taha-ahmed-mallick/NitroBurner-28c256/hardware/NitroBurner-28c256.kicad_sch

## KiCad design hardware/NitroBurner-28c256.kicad_sch (2026-06-18)

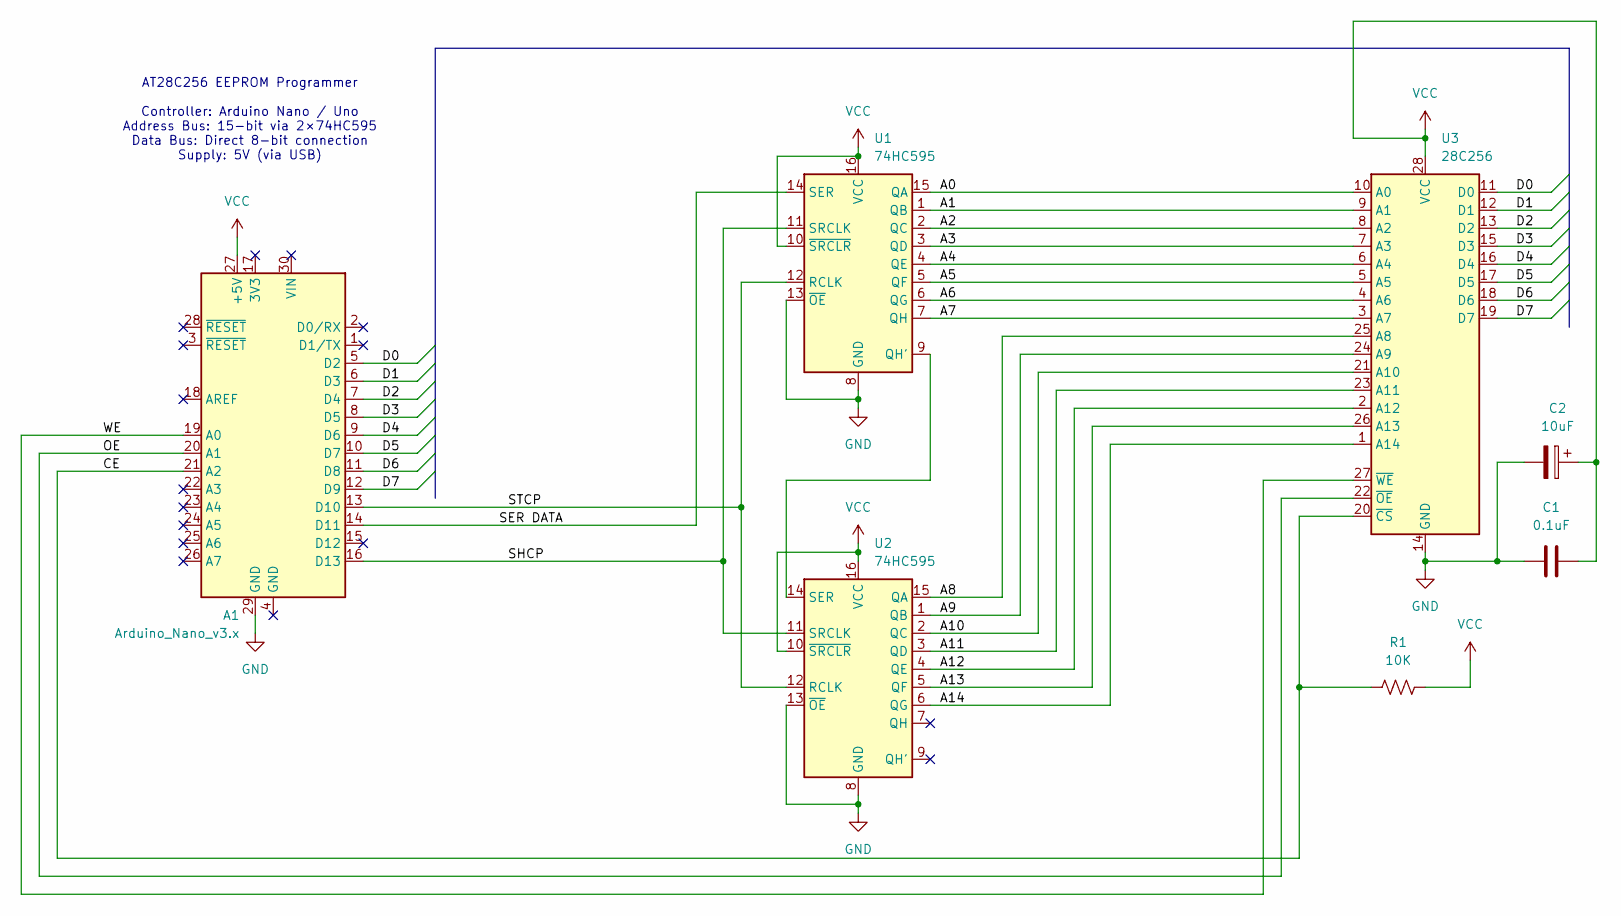
[picture p5: schematic NitroBurner-28c256.kicad_sch]

Parts:
A1: Arduino_Nano_v3.x; Arduino_Nano
C1: 0.1uF
C2: 10uF
R1: 10K
U1, U2: 74HC595
U3: 28C256

Connections:
A0: U1.15 (QA), U3.10 (A0)
A1: U1.1 (QB), U3.9 (A1)
A2: U1.2 (QC), U3.8 (A2)
A3: U1.3 (QD), U3.7 (A3)
A4: U1.4 (QE), U3.6 (A4)
A5: U1.5 (QF), U3.5 (A5)
A6: U1.6 (QG), U3.4 (A6)
A7: U1.7 (QH), U3.3 (A7)
A8: U2.15 (QA), U3.25 (A8)
A9: U2.1 (QB), U3.24 (A9)
A10: U2.2 (QC), U3.21 (A10)
A11: U2.3 (QD), U3.23 (A11)
A12: U2.4 (QE), U3.2 (A12)
A13: U2.5 (QF), U3.26 (A13)
A14: U2.6 (QG), U3.1 (A14)
CE: A1.21 (A2), R1.2, U3.20 (~CS)
D0: A1.5 (D2), U3.11 (D0)
D1: A1.6 (D3), U3.12 (D1)
D2: A1.7 (D4), U3.13 (D2)
D3: A1.8 (D5), U3.15 (D3)
D4: A1.9 (D6), U3.16 (D4)
D5: A1.10 (D7), U3.17 (D5)
D6: A1.11 (D8), U3.18 (D6)
D7: A1.12 (D9), U3.19 (D7)
GND: A1.29 (GND), C1.2, C2.2, U1.8 (GND), U1.13 (~OE), U2.8 (GND), U2.13 (~OE), U3.14 (GND)
unnamed: U1.9 (QH'), U2.14 (SER)
OE: A1.20 (A1), U3.22 (~OE)
SER DATA: A1.14 (D11), U1.14 (SER)
SHCP: A1.16 (D13), U1.11 (SRCLK), U2.11 (SRCLK)
STCP: A1.13 (D10), U1.12 (RCLK), U2.12 (RCLK)
VCC: A1.27 (+5V), C1.1, C2.1, R1.1, U1.10 (~SRCLR), U1.16 (VCC), U2.10 (~SRCLR), U2.16 (VCC), U3.28 (VCC)
WE: A1.19 (A0), U3.27 (~WE)

Notes on the sheet:
AT28C256 EEPROM Programmer Controller: Arduino Nano / Uno Address Bus: 15-bit via 2×74HC595 Data Bus: Direct 8-bit connection Supply: 5V (via USB)
